MurariDamera/power-buck-converter/ltspice/Buck_Converter_LTspice.asc

C1: cap; 680u
C2: cap; 100n
C3: cap; 220u
D1: diode; D1N5822
L1: ind; 33u
Rload: res; 1.667
V1: voltage; PWL(0 0 200u 12)
X1: LM2596_5P0_TRANS
Named nets: VIN, 0, SW, VOUT
.lib LM2596_5P0_TRANS.lib
.model D1N5822 D(IS=76.4u RS=0.025 N=1.05 CJO=300p VJ=0.34 M=0.35 EG=0.42 XTI=2 BV=40 IBV=1m TT=50n)
.tran 0 5m 0 1u
.measure TRAN Vout_avg AVG V(VOUT) FROM=4m TO=5m
.measure TRAN Vout_ripple PP V(VOUT) FROM=4.9m TO=5m
.measure TRAN IL_avg AVG I(L1) FROM=4m TO=5m
.backanno
LM2596-5.0 buck converter (12V to 5V) - LTspice validation of the KiCad design
Rload = 1.667 ohm models the 3A design-target load. Swap to 5 ohm for a 1A check.
